W3AXL/NRG-Anemometer-Display/kicad/input-sim.asc

A1: schmitt; Vhigh=3.3 Vt=1.2 Vh=.4 Trise=.1u Tfall=.1u
C1: cap; 0.1µ
D1: TVSdiode; SMBJ24CA
D2: zener; 1N750
R1: res; 100k
R2: res; 100k
R3: res; 10k
U1: UniversalOpamp2
V1: voltage; SINE(0 .1 4); Rser=650
V2: voltage; 3.3
Named nets: 0, Clamp, Input, Vcc, Amped, Buff
.tran 500m
