W3AXL/NRG-Anemometer-Display/nrg_code/fan.c

#define fan_width 32
#define fan_height 32
static const unsigned char fan1_bits[] = {
  0x00, 0x80, 0x00, 0x00, 0x00, 0xE0, 0x03, 0x00, 0x00, 0xF0, 0x0F, 0x00, 
  0x00, 0xF0, 0x0F, 0x00, 0x00, 0xF8, 0x1F, 0x00, 0x00, 0xF8, 0x1F, 0x00, 
  0x00, 0xF0, 0x3F, 0x00, 0x00, 0xF0, 0x3F, 0x00, 0x00, 0xE0, 0x1F, 0x00, 
  0x00, 0xC0, 0x1F, 0x00, 0x00, 0xC0, 0x1F, 0x00, 0x00, 0xC0, 0x0F, 0x00, 
  0x00, 0x00, 0x0C, 0x00, 0x00, 0x00, 0x00, 0x00, 0x00, 0x80, 0x01, 0x00, 
  0x80, 0xC7, 0x03, 0x00, 0xE0, 0xE7, 0x07, 0x00, 0xF0, 0xC7, 0x03, 0x00, 
  0xF8, 0xC7, 0xF3, 0x0F, 0xF8, 0x0F, 0xF0, 0x1F, 0xFC, 0x1F, 0xF8, 0x3F, 
  0xFC, 0x0F, 0xFE, 0x3F, 0xFC, 0x0F, 0xFC, 0x3F, 0xFC, 0x07, 0xFC, 0x3F, 
  0xFC, 0x03, 0xF8, 0x3F, 0xF8, 0x03, 0xF0, 0x1F, 0xF0, 0x01, 0xE0, 0x0F, 
  0x40, 0x00, 0x00, 0x00, 0x00, 0x00, 0x00, 0x00, 0x00, 0x00, 0x00, 0x00, 
  0x00, 0x00, 0x00, 0x00, 0x00, 0x00, 0x00, 0x00, };
static const unsigned char fan2_bits[] = {
  0x00, 0x00, 0x00, 0x00, 0x00, 0x00, 0x00, 0x00, 0x80, 0x0F, 0x00, 0x00, 
  0xC0, 0x3F, 0x00, 0x00, 0xE0, 0x7F, 0x00, 0x00, 0xE0, 0xFF, 0x00, 0x00, 
  0xF0, 0xFF, 0x00, 0x00, 0xE0, 0xFF, 0x01, 0x00, 0xE0, 0xFF, 0x01, 0x00, 
  0xC0, 0xFF, 0x01, 0x00, 0x00, 0xFF, 0x01, 0x00, 0x00, 0x1E, 0x00, 0x0C, 
  0x00, 0x08, 0x00, 0x3F, 0x00, 0x80, 0x80, 0x7F, 0x00, 0xE0, 0xF1, 0x7F, 
  0x00, 0xE0, 0xF3, 0xFF, 0x00, 0xE0, 0xF3, 0x7F, 0x00, 0xE4, 0xF1, 0x7F, 
  0x00, 0x87, 0xF8, 0x3F, 0x80, 0x0F, 0xF8, 0x3F, 0xC0, 0x3F, 0xE0, 0x0F, 
  0xE0, 0x3F, 0x00, 0x03, 0xE0, 0x3F, 0x00, 0x00, 0xE0, 0x3F, 0x00, 0x00, 
  0xE0, 0x3F, 0x00, 0x00, 0xE0, 0x3F, 0x00, 0x00, 0xE0, 0x3F, 0x00, 0x00, 
  0xE0, 0x3F, 0x00, 0x00, 0xC0, 0x1F, 0x00, 0x00, 0x80, 0x0F, 0x00, 0x00, 
  0x00, 0x00, 0x00, 0x00, 0x00, 0x00, 0x00, 0x00, };
static const unsigned char fan3_bits[] = {
  0x00, 0x00, 0x00, 0x00, 0x00, 0x00, 0x00, 0x00, 0x00, 0x00, 0x00, 0x00, 
  0x00, 0x00, 0x00, 0x00, 0x00, 0x00, 0x00, 0x02, 0xF0, 0x07, 0x80, 0x0F, 
  0xF8, 0x0F, 0xC0, 0x1F, 0xFC, 0x1F, 0xC0, 0x3F, 0xFC, 0x3F, 0xE0, 0x3F, 
  0xFC, 0x3F, 0xF0, 0x3F, 0xFC, 0x7F, 0xF0, 0x3F, 0xFC, 0x1F, 0xF8, 0x3F, 
  0xF8, 0x0F, 0xF0, 0x1F, 0xF0, 0xCF, 0xE3, 0x1F, 0x00, 0xC0, 0xE3, 0x0F, 
  0x00, 0xE0, 0xE7, 0x07, 0x00, 0xC0, 0xE3, 0x01, 0x00, 0x80, 0x01, 0x00, 
  0x00, 0x00, 0x00, 0x00, 0x00, 0x30, 0x00, 0x00, 0x00, 0xF0, 0x03, 0x00, 
  0x00, 0xF8, 0x03, 0x00, 0x00, 0xF8, 0x03, 0x00, 0x00, 0xF8, 0x07, 0x00, 
  0x00, 0xFC, 0x0F, 0x00, 0x00, 0xFC, 0x0F, 0x00, 0x00, 0xF8, 0x1F, 0x00, 
  0x00, 0xF8, 0x1F, 0x00, 0x00, 0xF0, 0x0F, 0x00, 0x00, 0xF0, 0x0F, 0x00, 
  0x00, 0xC0, 0x07, 0x00, 0x00, 0x00, 0x01, 0x00, };
static const unsigned char fan4_bits[] = {
  0x00, 0x00, 0x00, 0x00, 0x00, 0x00, 0x00, 0x00, 0x00, 0x00, 0xF0, 0x01, 
  0x00, 0x00, 0xF8, 0x03, 0x00, 0x00, 0xFC, 0x07, 0x00, 0x00, 0xFC, 0x07, 
  0x00, 0x00, 0xFC, 0x07, 0x00, 0x00, 0xFC, 0x07, 0x00, 0x00, 0xFC, 0x07, 
  0x00, 0x00, 0xFC, 0x07, 0xC0, 0x00, 0xFC, 0x07, 0xF0, 0x07, 0xFC, 0x03, 
  0xFC, 0x1F, 0xF0, 0x01, 0xFC, 0x1F, 0xE1, 0x00, 0xFE, 0x8F, 0x27, 0x00, 
  0xFE, 0xCF, 0x07, 0x00, 0xFF, 0xCF, 0x07, 0x00, 0xFE, 0x8F, 0x07, 0x00, 
  0xFE, 0x01, 0x01, 0x00, 0xFC, 0x00, 0x10, 0x00, 0x30, 0x00, 0x78, 0x00, 
  0x00, 0x80, 0xFF, 0x00, 0x00, 0x80, 0xFF, 0x03, 0x00, 0x80, 0xFF, 0x07, 
  0x00, 0x80, 0xFF, 0x07, 0x00, 0x00, 0xFF, 0x0F, 0x00, 0x00, 0xFF, 0x07, 
  0x00, 0x00, 0xFE, 0x07, 0x00, 0x00, 0xFC, 0x03, 0x00, 0x00, 0xF0, 0x01, 
  0x00, 0x00, 0x00, 0x00, 0x00, 0x00, 0x00, 0x00, };
