W3AXL/NRG-Anemometer-Display/nrg_code/fan3d.c

#define fan_width 32
#define fan_height 16
static const unsigned char fan1_bits[] = {
  0x00, 0x00, 0x00, 0x00, 0x00, 0xC0, 0x01, 0x00, 0x00, 0xE0, 0x0F, 0x00, 
  0x00, 0xC0, 0x0F, 0x00, 0x00, 0x00, 0x06, 0x00, 0x00, 0x80, 0x01, 0x00, 
  0xC0, 0xCF, 0x03, 0x00, 0xF0, 0x0F, 0xF0, 0x0F, 0xF8, 0x0F, 0xFE, 0x1F, 
  0xFC, 0x07, 0xFC, 0x3F, 0xF8, 0x01, 0xF0, 0x1F, 0x00, 0x00, 0x00, 0x00, 
  0x00, 0x00, 0x00, 0x00, 0x00, 0x00, 0x00, 0x00, 0x00, 0x00, 0x00, 0x00, 
  0x00, 0x00, 0x00, 0x00, };
static const unsigned char fan2_bits[] = {
  0x00, 0x00, 0x00, 0x00, 0x00, 0x00, 0x00, 0x00, 0x00, 0x00, 0x7E, 0x00, 
  0x00, 0x00, 0xFE, 0x00, 0xC0, 0x07, 0x7E, 0x00, 0xF8, 0x8F, 0x11, 0x00, 
  0xFC, 0xCF, 0x03, 0x00, 0xFC, 0x01, 0x00, 0x00, 0x00, 0x80, 0x3F, 0x00, 
  0x00, 0x80, 0xFF, 0x01, 0x00, 0x80, 0xFF, 0x03, 0x00, 0x80, 0xFF, 0x07, 
  0x00, 0x00, 0xFE, 0x03, 0x00, 0x00, 0xF0, 0x00, 0x00, 0x00, 0x00, 0x00, 
  0x00, 0x00, 0x00, 0x00, };
static const unsigned char fan3_bits[] = {
  0x00, 0x00, 0x00, 0x00, 0x00, 0x00, 0x00, 0x00, 0x00, 0x00, 0x00, 0x00, 
  0xC0, 0x3F, 0xF0, 0x03, 0xF0, 0x7F, 0xF8, 0x07, 0xE0, 0x8F, 0xF1, 0x07, 
  0x00, 0xC0, 0xF3, 0x01, 0x00, 0x00, 0x00, 0x00, 0x00, 0xF0, 0x03, 0x00, 
  0x00, 0xF8, 0x03, 0x00, 0x00, 0xFC, 0x0F, 0x00, 0x00, 0xFC, 0x1F, 0x00, 
  0x00, 0xF8, 0x1F, 0x00, 0x00, 0xF0, 0x0F, 0x00, 0x00, 0xC0, 0x03, 0x00, 
  0x00, 0x00, 0x00, 0x00, };
static const unsigned char fan4_bits[] = {
  0x00, 0x00, 0x00, 0x00, 0x00, 0x00, 0x00, 0x00, 0x00, 0xFE, 0x00, 0x00, 
  0x00, 0xFF, 0x01, 0x00, 0x00, 0x78, 0x00, 0x00, 0x00, 0x80, 0xE1, 0x1F, 
  0x00, 0xC0, 0xF3, 0x3F, 0x00, 0x0E, 0xF0, 0x1F, 0x80, 0x7F, 0xC0, 0x07, 
  0xC0, 0x7F, 0x00, 0x00, 0xC0, 0x7F, 0x00, 0x00, 0xE0, 0x7F, 0x00, 0x00, 
  0xC0, 0x3F, 0x00, 0x00, 0x80, 0x0F, 0x00, 0x00, 0x00, 0x00, 0x00, 0x00, 
  0x00, 0x00, 0x00, 0x00, };
